RADARC/Modular-PA-Controller/Kicad/PA_Power_V1/RLab Keyboard/ki-lime-pi-pico-2.1.2/_md-assets/images/footprints.png

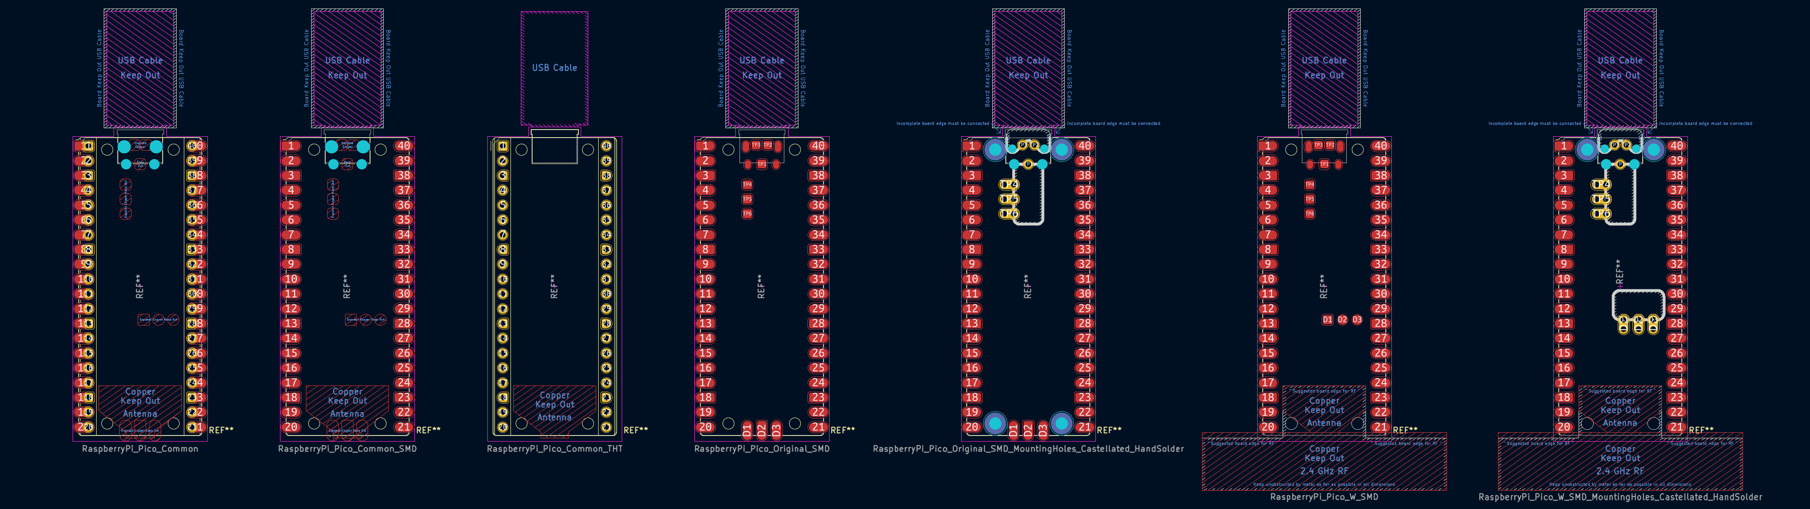
Kicad/PA_Power_V1/RLab Keyboard/ki-lime-pi-pico-2.1.2/_md-assets/images/footprints.png
